AlanFord/LEDtester/avr/lcd.c

/*
 * ----------------------------------------------------------------------------
 * "THE BEER-WARE LICENSE" (Revision 42):
 * <joerg@FreeBSD.ORG> wrote this file.  As long as you retain this notice you
 * can do whatever you want with this stuff. If we meet some day, and you think
 * this stuff is worth it, you can buy me a beer in return.        Joerg Wunsch
 * ----------------------------------------------------------------------------
 *
 * Stdio demo, upper layer of LCD driver.
 *
 * $Id$
 */

#include "lcdDefines.h"

#include <stdbool.h>
#include <stdint.h>
#include <stdio.h>

#include <avr/io.h>

#include <util/delay.h>

#include "hd44780.h"
#include "lcd.h"
#include "USART.h"

/*
 * Setup the LCD controller.  First, call the hardware initialization
 * function, then adjust the display attributes we want.
 */
void
lcd_init(void)
{

  hd44780_init();

  /*
   * Clear the display.
   */
  hd44780_outcmd(HD44780_CLR);
  hd44780_wait_ready(true);

  /*
   * Entry mode: auto-increment address counter, no display shift in
   * effect.
   */
  hd44780_outcmd(HD44780_ENTMODE(1, 0));
  hd44780_wait_ready(false);

  /*
   * Enable display, activate non-blinking cursor.
   */
  hd44780_outcmd(HD44780_DISPCTL(1, 1, 0));
  hd44780_wait_ready(false);
}

/*
 * Send character c to the LCD display.  After a '\n' has been seen,
 * the next character will first clear the display.
 */
int
lcd_putchar(char c, FILE *unused)
{
  static bool nl_seen;
  //debugString("putchar called\r\n");   // test the USART connection

  if (nl_seen && c != '\n')
    {
      /*
       * First character after newline, clear display and home cursor.
       */
      hd44780_wait_ready(false);
      hd44780_outcmd(HD44780_CLR);
      hd44780_wait_ready(false);
      hd44780_outcmd(HD44780_HOME);
      hd44780_wait_ready(true);
      hd44780_outcmd(HD44780_DDADDR(0));

      nl_seen = false;
    }
  if (c == '\n')
    {
      nl_seen = true;
    }
  else
    {
      hd44780_wait_ready(false);
      hd44780_outdata(c);
    }

  return 0;
}

// manually clear screen
void lcd_clear(void)
{
    hd44780_wait_ready(false);
    hd44780_outcmd(HD44780_CLR);
    hd44780_wait_ready(false);
    hd44780_outcmd(HD44780_HOME);
    hd44780_wait_ready(true);
}

// put a 5x8 character into memory
void put_char(const unsigned char item[], int charIndex)
{
    int i;
    unsigned char characterCode = (charIndex & 0b111);
    unsigned char cgramAddr = (characterCode << 3);
    // load address of character generator RAM (CGRAM)
    for (i=0; i<8; i++){
        hd44780_wait_ready(false);
        hd44780_outcmd(HD44780_CGADDR(cgramAddr));
        hd44780_wait_ready(false);
        hd44780_outdata(item[i]);
        cgramAddr++;
    }
    hd44780_wait_ready(false);
}

void startFirstRow(void)
{
    hd44780_wait_ready(false);
    hd44780_outcmd(HD44780_DDADDR(0x00));
    hd44780_wait_ready(false);
}

void startSecondRow(void)
{
    hd44780_wait_ready(false);
    hd44780_outcmd(HD44780_DDADDR(0x40));
    hd44780_wait_ready(false);
}
